jstiefel/esp32_komoot_ble/images/img1.jpg

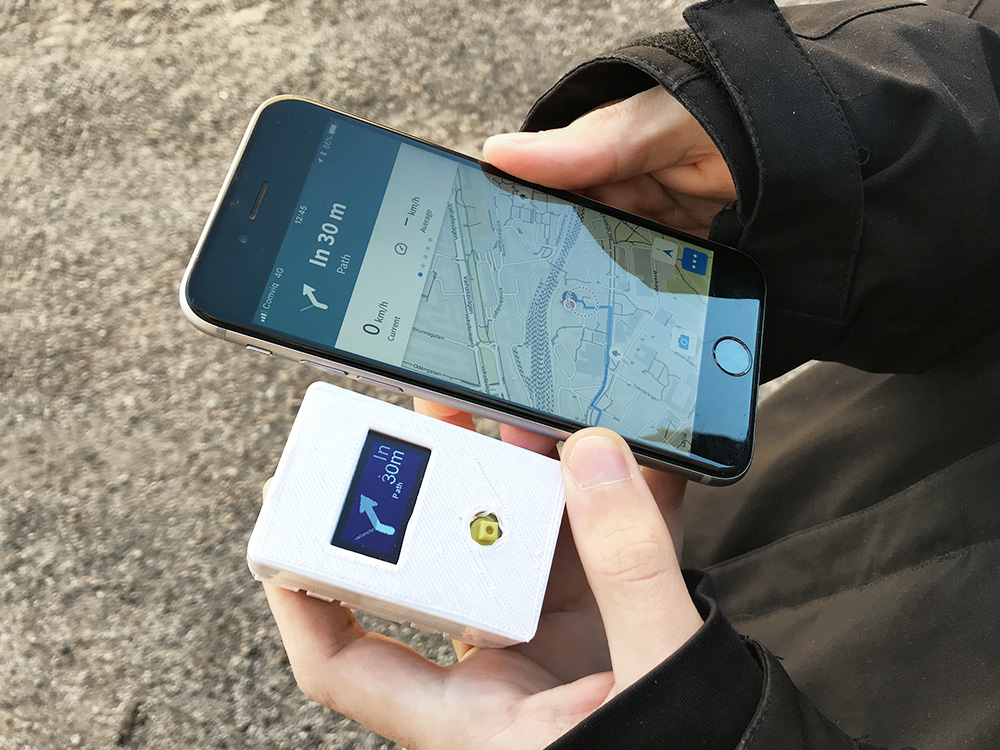
images/img1.jpg
