jstiefel/esp32_komoot_ble/src/symbols.cpp

/*
 * 	symbols.cpp
 *
 *	Version: 1.0.0
 *  Created on: Dec 14, 2018
 *  Author: Julian Stiefel
 *  License: BSD 3-Clause
 *  Description: File containing the bitmaps for direction arrows.
 */

#include "symbols.h"

const uint8_t ic_nav_arrow_finish[] PROGMEM = {
  0x00, 0x00, 0x00, 0x00, 0x00, 0x00, 0x00, 0x00, 0x00, 0x00, 0x00, 0x00,
  0x00, 0x00, 0x00, 0x00, 0x00, 0x00, 0xC0, 0xBD, 0xFF, 0x01, 0x00, 0x00,
  0x00, 0x00, 0xE0, 0xFF, 0x5A, 0x03, 0x00, 0x00, 0x00, 0x00, 0xE0, 0xFF,
  0x00, 0x01, 0x00, 0x00, 0x00, 0x00, 0xE0, 0xFF, 0x80, 0x01, 0x00, 0x00,
  0x00, 0x00, 0xE0, 0x7F, 0x80, 0x00, 0x00, 0x00, 0x00, 0x00, 0xE0, 0xFF,
  0x80, 0x00, 0x00, 0x00, 0x00, 0x00, 0xE0, 0x7F, 0x40, 0x00, 0x00, 0x00,
  0x00, 0x00, 0xE0, 0xFF, 0x40, 0x00, 0x00, 0x00, 0x00, 0x00, 0x20, 0x84,
  0x7F, 0x00, 0x00, 0x00, 0x00, 0x00, 0x20, 0x00, 0x7F, 0x00, 0x00, 0x00,
  0x00, 0x00, 0x60, 0x80, 0xFF, 0x00, 0x00, 0x00, 0x00, 0x00, 0x20, 0x00,
  0xFF, 0x00, 0x00, 0x00, 0x00, 0x00, 0x20, 0x80, 0xFF, 0x00, 0x00, 0x00,
  0x00, 0x00, 0x60, 0x00, 0xFF, 0x01, 0x00, 0x00, 0x00, 0x00, 0x20, 0x80,
  0xFF, 0x01, 0x00, 0x00, 0x00, 0x00, 0xE0, 0xFF, 0xFF, 0x03, 0x00, 0x00,
  0x00, 0x00, 0x20, 0x00, 0x00, 0x00, 0x00, 0x00, 0x00, 0x00, 0x60, 0x00,
  0x00, 0x00, 0x00, 0x00, 0x00, 0x00, 0x20, 0x00, 0x00, 0x00, 0x00, 0x00,
  0x00, 0x00, 0x20, 0x00, 0x00, 0x00, 0x00, 0x00, 0x00, 0x00, 0x60, 0x00,
  0x00, 0x00, 0x00, 0x00, 0x00, 0x00, 0x20, 0x00, 0x00, 0x00, 0x00, 0x00,
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
  0x00, 0x80, 0x48, 0x00, 0x00, 0x00, 0xFF, 0x00, 0x00, 0x40, 0x00, 0x00,
  0x00, 0x80, 0xFF, 0x01, 0x00, 0x60, 0x00, 0x00, 0x00, 0x00, 0xFF, 0x01,
  0x00, 0xC0, 0x00, 0x00, 0x00, 0x00, 0xFF, 0x01, 0x00, 0x40, 0x00, 0x00,
  0x00, 0x00, 0xFF, 0x03, 0x00, 0x70, 0x00, 0x00, 0x00, 0x00, 0xFE, 0x07,
  0x00, 0x20, 0x00, 0x00, 0x00, 0x00, 0xFE, 0x0F, 0x00, 0x30, 0x00, 0x00,
  0x00, 0x00, 0xFC, 0x3F, 0x00, 0x1C, 0x00, 0x00, 0x00, 0x00, 0xFC, 0xFF,
  0x03, 0x0C, 0x00, 0x00, 0x00, 0x00, 0xF8, 0xFF, 0x0F, 0x03, 0x00, 0x00,
  0x00, 0x00, 0xF0, 0xFF, 0x8F, 0x03, 0x00, 0x00, 0x00, 0x00, 0xE0, 0xFF,
  0xFF, 0x00, 0x00, 0x00, 0x00, 0x00, 0xC0, 0xFF, 0x1F, 0x00, 0x00, 0x00,
  0x00, 0x00, 0x80, 0xFF, 0x1F, 0x00, 0x00, 0x00, 0x00, 0x00, 0x00, 0xFE,
  0x1F, 0x00, 0x00, 0x00, 0x00, 0x00, 0x00, 0xF8, 0x1F, 0x00, 0x00, 0x00,
  0x00, 0x00, 0x00, 0xF0, 0x1F, 0x00, 0x00, 0x00, 0x00, 0x00, 0x00, 0xF0,
  0x1F, 0x00, 0x00, 0x00, 0x00, 0x00, 0x00, 0xF0, 0x1F, 0x00, 0x00, 0x00,
  0x00, 0x00, 0x00, 0xF0, 0x1F, 0x00, 0x00, 0x00, 0x00, 0x00, 0x00, 0xF0,
  0x1F, 0x00, 0x00, 0x00, 0x00, 0x00, 0x00, 0xF0, 0x1F, 0x00, 0x00, 0x00,
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
  };

const uint8_t not_defined[] PROGMEM = {};

const uint8_t *nav_symbols[31] PROGMEM = {
	//goto_start not defined yet
	//two dimensional array is actually a one dimensional array of pointers
	not_defined,
	ic_nav_arrow_keep_going,
	ic_nav_arrow_start,
	ic_nav_arrow_finish,
	ic_nav_arrow_keep_left,
	ic_nav_arrow_turn_left,
	ic_nav_arrow_turn_hard_left,
	ic_nav_arrow_turn_hard_right,
	ic_nav_arrow_turn_right,
	ic_nav_arrow_keep_right,
	ic_nav_arrow_fork_right,
	ic_nav_arrow_fork_left,
	ic_nav_arrow_uturn,
	not_defined,
	not_defined,
	ic_nav_roundabout_exit_cw,
	ic_nav_roundabout_exit_ccw,
	ic_nav_roundabout_ccw1_1,
	ic_nav_roundabout_ccw1_2,
	ic_nav_roundabout_ccw1_3,
	ic_nav_roundabout_ccw2_2,
	ic_nav_roundabout_ccw2_3,
	ic_nav_roundabout_ccw3_3,
	ic_nav_roundabout_cw1_1,
	ic_nav_roundabout_cw1_2,
	ic_nav_roundabout_cw1_3,
	ic_nav_roundabout_cw2_2,
	ic_nav_roundabout_cw2_3,
	ic_nav_roundabout_cw3_3,
	ic_nav_roundabout_fallback,
	ic_nav_outof_route
  };
